kerikun11/kerigokbd/hardware/kerigokbd/pcb_20250208/images/kerigokbd_v1_pcb_back.jpg

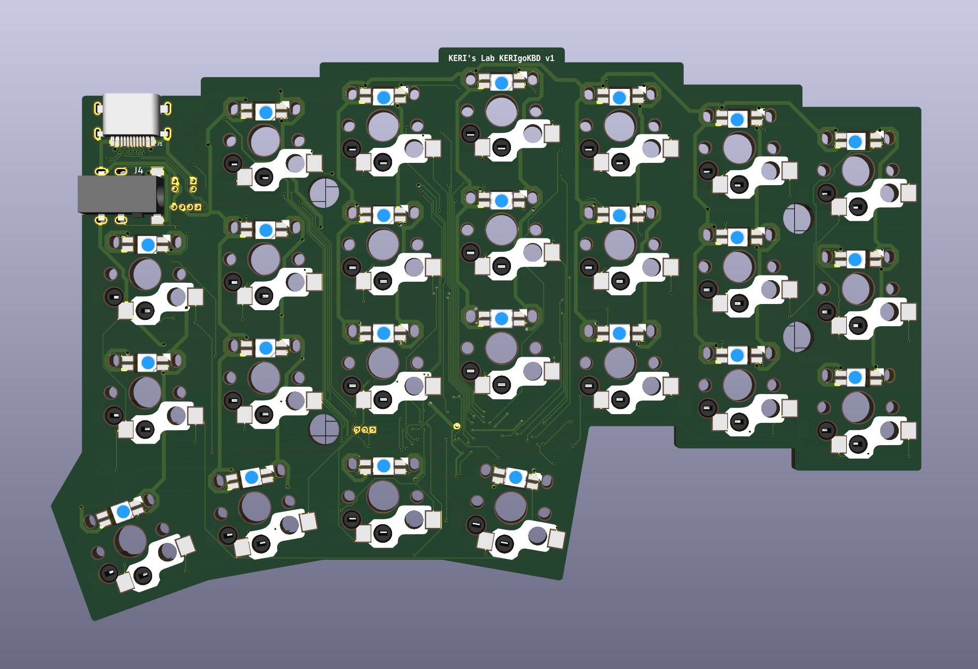
hardware/kerigokbd/pcb_20250208/images/kerigokbd_v1_pcb_back.jpg
