kerikun11/kerigokbd/hardware/kerigokbd/pcb_20250208/images/kerigokbd_v1_pcb_front.jpg

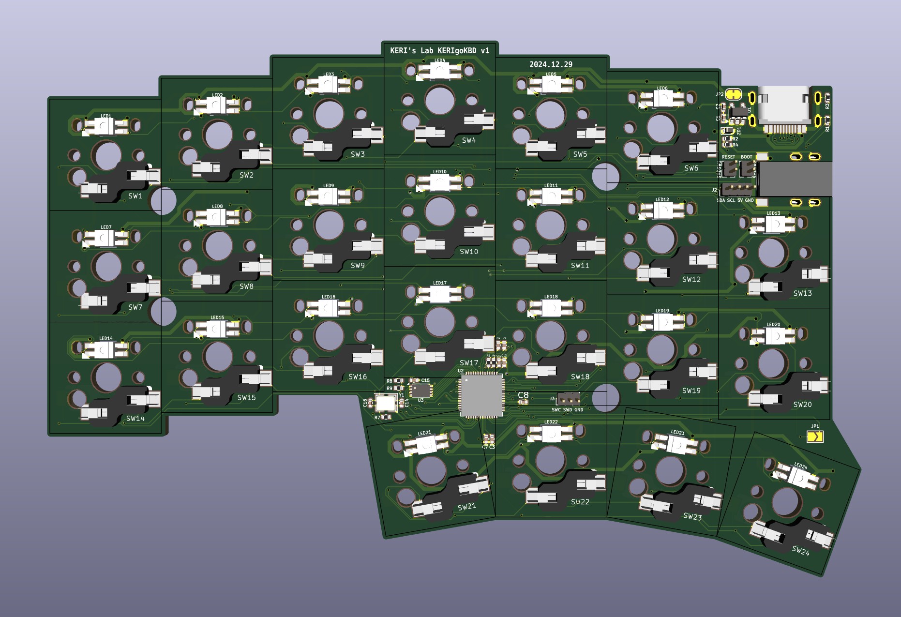
hardware/kerigokbd/pcb_20250208/images/kerigokbd_v1_pcb_front.jpg
