kerikun11/kerigokbd/software/qmk/keyboards/kerigokbd/kerigokbd_corne_v4/images/kerigokbd_corne_v4_shining.jpg

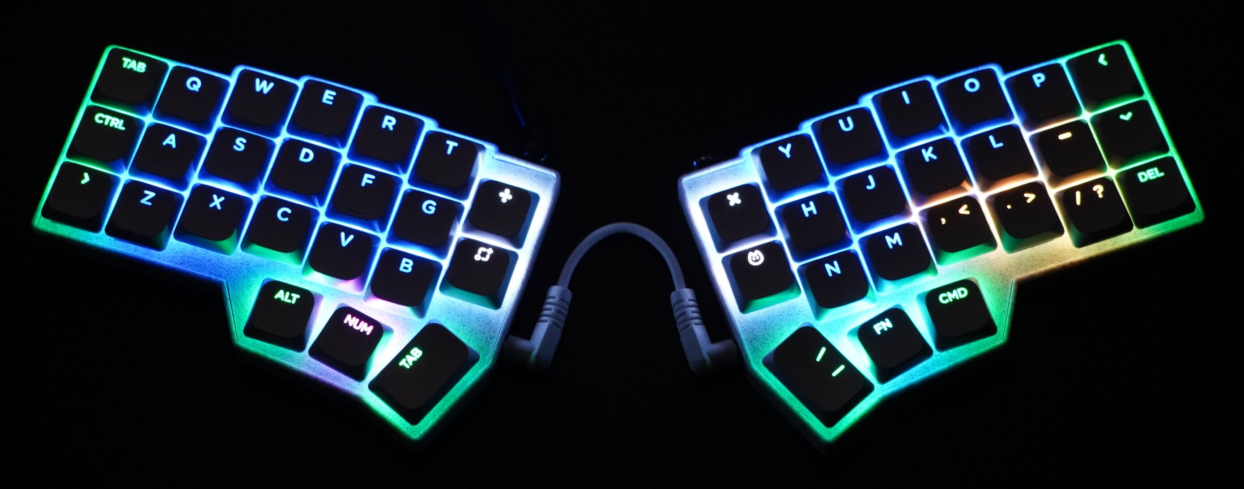
software/qmk/keyboards/kerigokbd/kerigokbd_corne_v4/images/kerigokbd_corne_v4_shining.jpg
